spuder/OpenSpool/images/Change_fillament.png

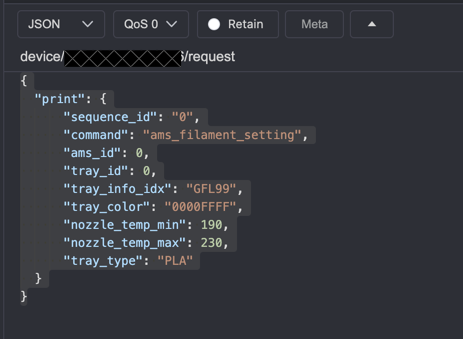
images/Change_fillament.png
