spuder/OpenSpool/images/LED2.png

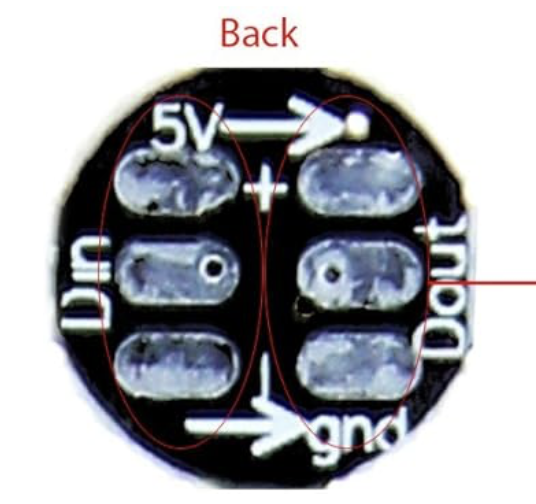
images/LED2.png
