spuder/OpenSpool/images/mqttx.png

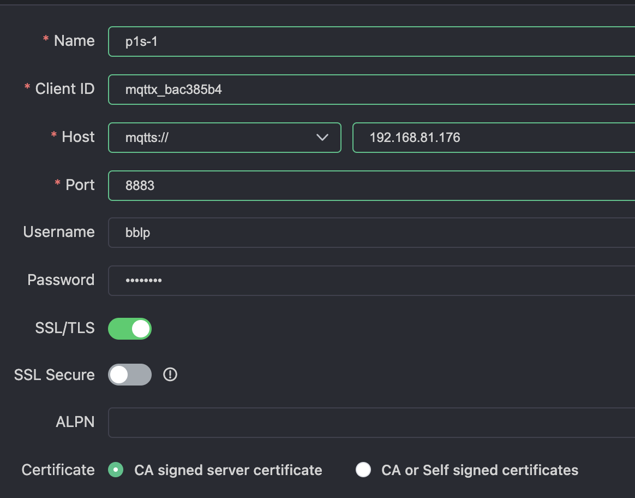
images/mqttx.png
