spuder/OpenSpool/images/PCB1.png

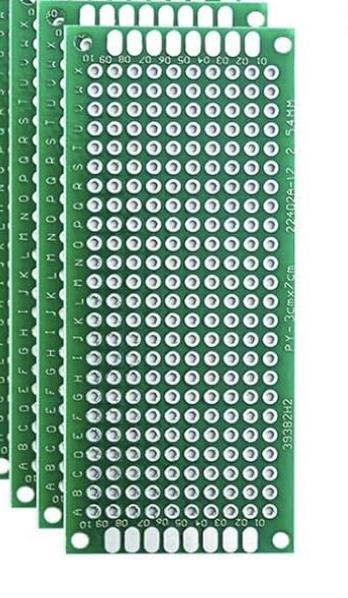
images/PCB1.png
