spuder/OpenSpool/images/pn532-large.png

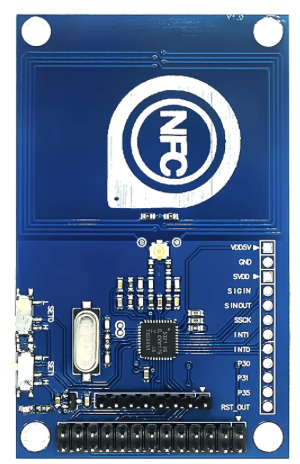
images/pn532-large.png
