spuder/OpenSpool/images/PSRAM.png

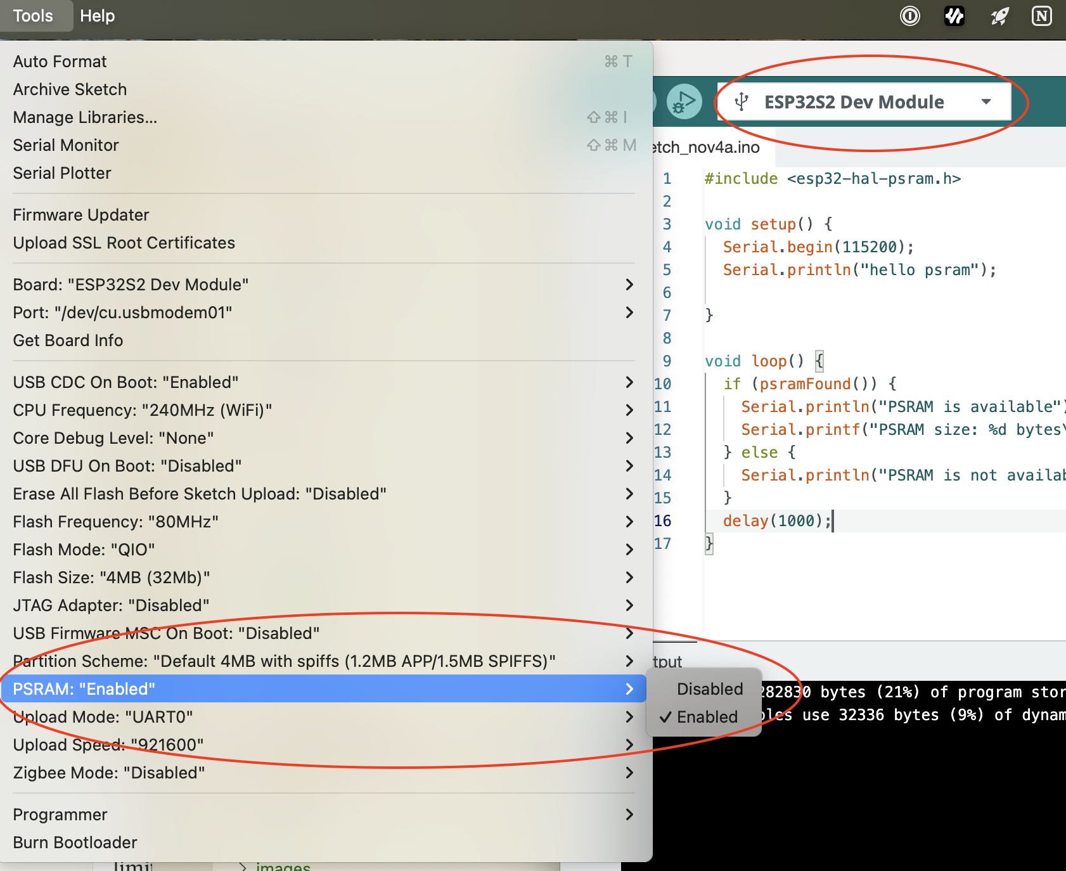
images/PSRAM.png
