spuder/OpenSpool/images/RainbowReel.png

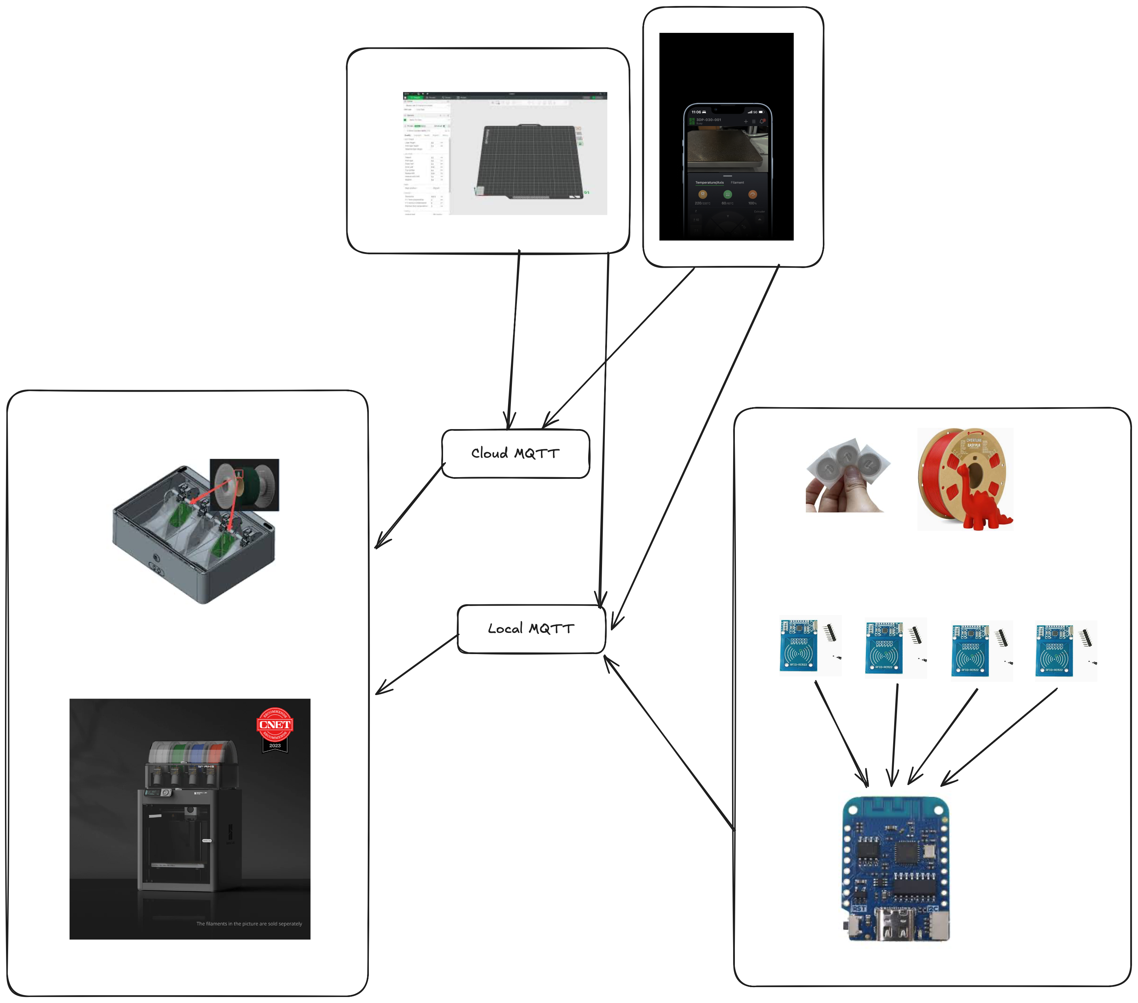
images/RainbowReel.png
