spuder/OpenSpool/images/Simulator Screenshot - iPhone SE (3rd generation) - 2025-01-03 at 22.12.15.png

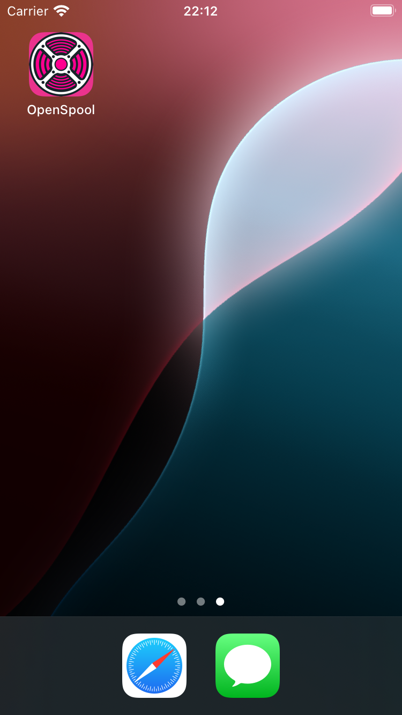
images/Simulator Screenshot - iPhone SE (3rd generation) - 2025-01-03 at 22.12.15.png
