spuder/OpenSpool/images/tindie/IMG_6108.png

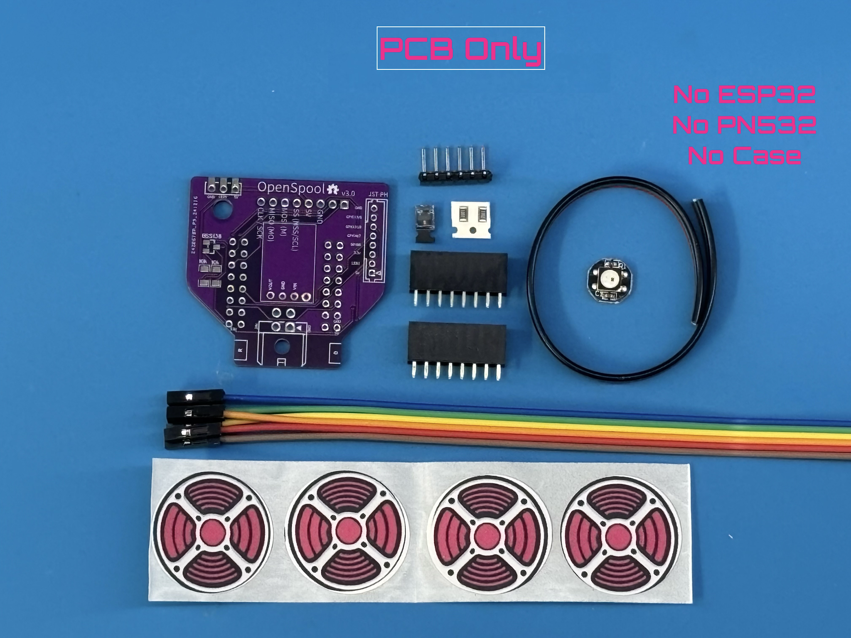
images/tindie/IMG_6108.png
