spuder/OpenSpool/images/tindie/IMG_6125.jpg

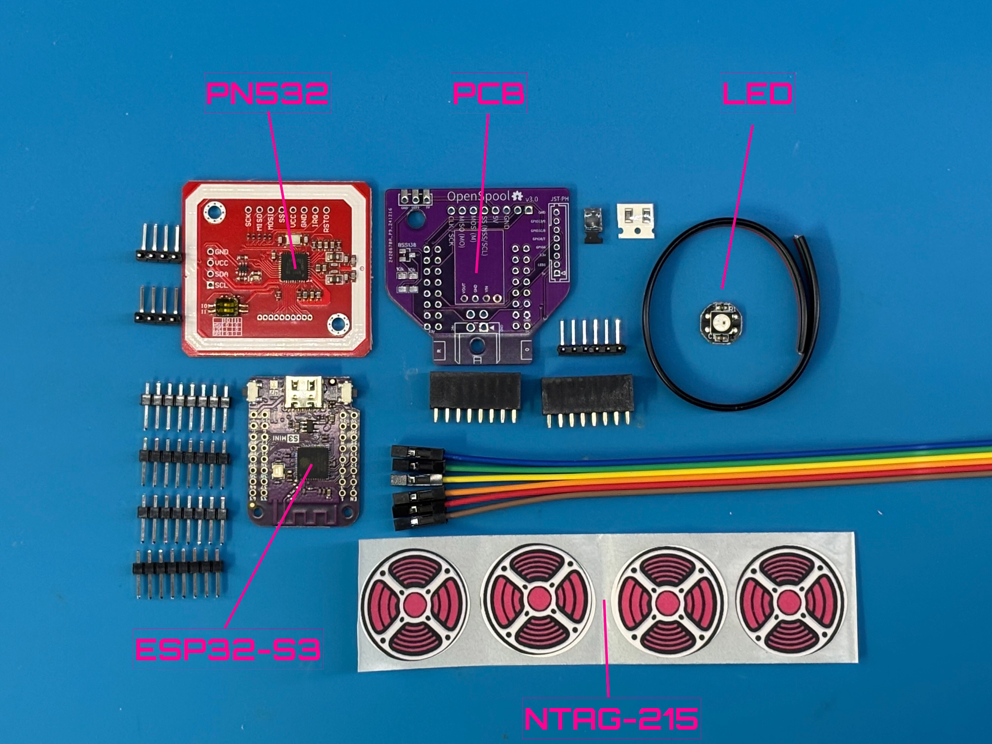
images/tindie/IMG_6125.jpg
