spuder/OpenSpool/hardware/openspool-mini/v2.0/Schematic_OpenSpool_2024-11-19.pdf

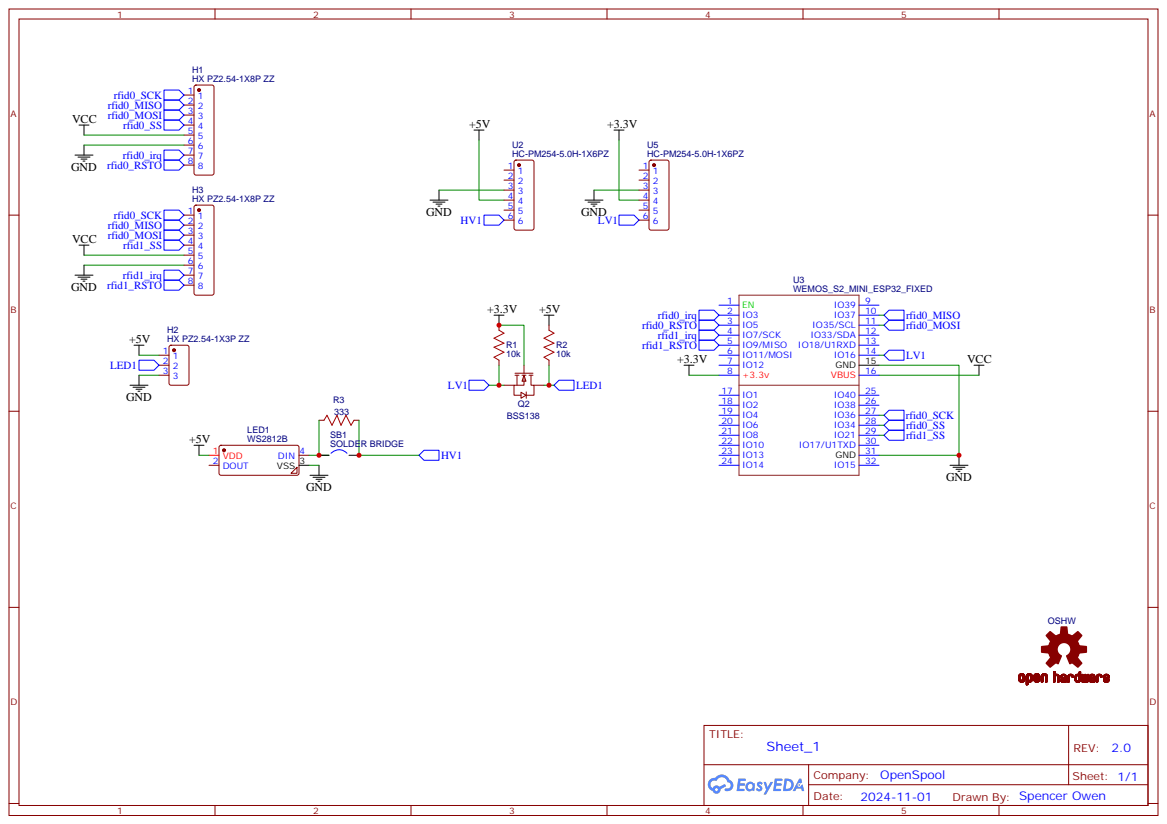
[picture p67: page 1]
